Universidad-Cenfotec/Sumobot/códigos_de_ejemplo/Libreria HCSR04/8.x (DEPRECADO)/README.md

> ⚠️ **AVISO IMPORTANTE – VERSIÓN DEPRECADA** ⚠️  
> **Sumobot – Universidad CENFOTEC**

Las **primeras versiones del Sumobot de la Universidad CENFOTEC** utilizaban **IdeaBoards de CRCibernética** con firmware **CircuitPython 8.2.0**.

Actualmente, **esta versión y toda la rama 8.x de CircuitPython se encuentran deprecadas**, por lo que:
- ❌ No reciben soporte oficial
- ❌ No se recomienda su uso en nuevos desarrollos

Asimismo, **CRCibernética ya distribuye las placas IdeaBoard con versiones de firmware actuales**, alineadas con CircuitPython 9.x y superiores.

### Estado de esta librería
La librería correspondiente a **CircuitPython 8.x** se considera **obsoleta**, **Archivada** y es conservada únicamente con fines de **documentación histórica** y **compatibilidad retroactiva**

No se realizarán mejoras ni correcciones sobre esta versión.

### ✅ Recomendación
Se recomienda **actualizar el firmware de la IdeaBoard** a una versión moderna de CircuitPython para:
- Mantener compatibilidad con el desarrollo actual del Sumobot  
- Acceder a mejoras de rendimiento y estabilidad  
- Asegurar soporte futuro

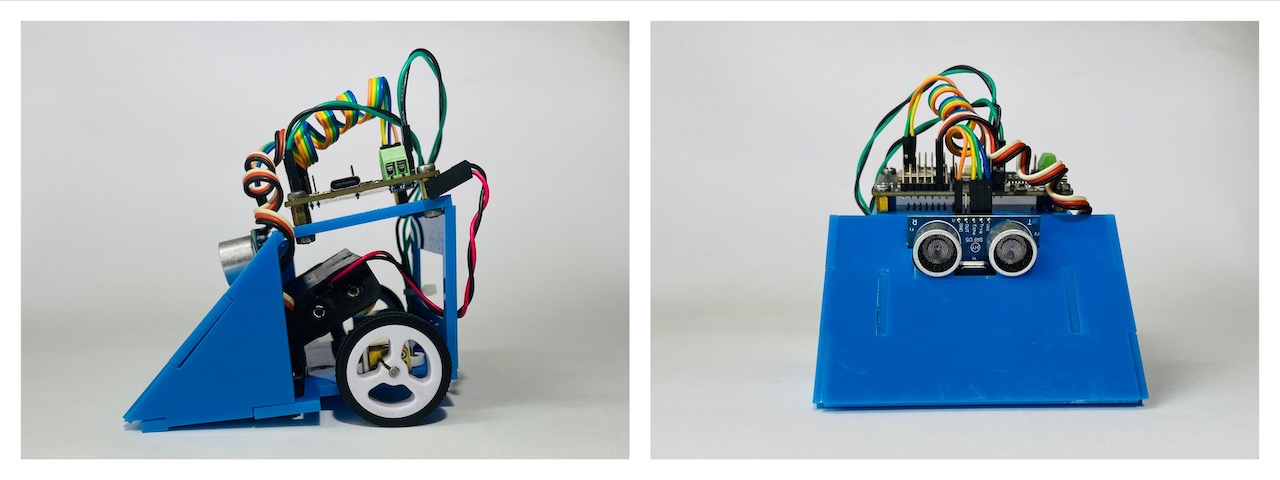
[picture p18: imagenes/SumoBot_1.JPG]
Sumobot Legacy
