Universidad-Cenfotec/Sumobot/espiritu_sumobot.md

# El espíritu del Torneo Sumobot 

## Sobre el Sumobot

**Un espacio para aprender y disfrutar**

El Sumobot no es solo una competencia.
Es un espacio donde venimos a aprender, probar ideas y pasarla bien.

Aquí construir es importante.
Pensar es importante.
Pero también lo es jugar.

En el Sumobot somos:

* Personas que construyen (**homo faber**)
* Personas que piensan (**homo sapiens**)
* Personas que disfrutan el juego (**homo ludens**)
* Personas que crean con tecnología (**homo ciberneticus**)

### ¿Qué significa competir aquí?

Aunque nuestros robots “luchan”, esto no es violencia.
Es una forma de poner a prueba ideas.

Cada combate es una oportunidad para aprender algo nuevo:
qué funciona, qué no, y qué podemos mejorar.

Aquí no se trata solo de ganar,
se trata de **entender lo que hacemos**.

### ¿Y si hay problemas?

En el Sumobot, los problemas se resuelven **hablando**.

* Las reglas no son solo para obedecerlas, son para entenderlas
* Si algo no es justo, se puede conversar
* Escuchar a los demás es parte del juego
* Resolver conflictos también es aprender

No estamos aquí para pelear entre nosotros,
estamos aquí para aprender juntos.

### Lo importante

* Disfrutar lo que hacemos
* Aprender de los errores
* Respetar a los demás
* Intentar cosas nuevas

Al final, lo más valioso no es el resultado,
es lo que aprendimos en el camino.
