Universidad-Cenfotec/Sumobot/instala_thonny.md

# **Cómo instalar Thonny y preparar el Sumobot para programarlo**

1. **Descargar Thonny**

   * Abre tu navegador y busca **“Thonny Python”**.
   * Ingresa al sitio oficial y descarga la versión correspondiente a tu sistema operativo (Windows, Mac o Linux).

2. **Instalar Thonny**

   * Ejecuta el instalador descargado.
   * En el asistente de instalación, presiona **Next** y acepta los términos.
   * Mantén las configuraciones por defecto (no es necesario cambiar nada).
   * Activa la opción para crear un acceso directo en el escritorio y haz clic en **Install**.
   * Al finalizar, presiona **Finish**.

3. **Abrir Thonny**

   * Busca **Thonny** en el menú de inicio y ábrelo.
   * La primera vez, selecciona el idioma (inglés o español según tu preferencia).

4. **Configurar el intérprete**

   * En el menú superior selecciona: **Tools → Options → Interpreter**.
   * Cambia el intérprete a **“CircuitPython (generic)”**.

5. **Conectar el Sumobot**

   * Conecta el cable **USB-C** al puerto del Sumobot.
   * Conecta el otro extremo **USB** a tu computadora.
   * Verifica que el dispositivo aparezca en el listado de puertos dentro de Thonny.

6. **Explorar los archivos del Sumobot**

   * En el panel de archivos de Thonny verás dos ubicaciones: tu computadora y el dispositivo **CircuitPython**.
   * Haz doble clic en el archivo **`code.py`** para abrir el programa que controla el robot.

7. **Listo para programar**

   * A partir de este punto, podrás modificar el archivo `code.py` y cargar tus programas al Sumobot.

**Tip:** Trabaja únicamente sobre el archivo `code.py` para mantener el funcionamiento correcto del robot.
