Universidad-Cenfotec/Sumobot/uso_thonny.md

# **Cómo programar el Sumobot usando Thonny**

1. **Conectar el Sumobot a la computadora**

   * Usa el cable incluido con el Sumobot.
   * Conecta el extremo **USB-C** al puerto del Sumobot.
   * Conecta el otro extremo **USB** a tu computadora.
   * En algunas computadoras escucharás un sonido al reconocer el dispositivo.

2. **Abrir Thonny**

   * Ejecuta el programa **Thonny** (ícono con las letras *Th*).

3. **Configurar el intérprete**

   * En el menú superior selecciona: **Herramientas → Opciones**.
   * Ve a la pestaña **Intérprete**.
   * Selecciona el puerto donde está conectado el Sumobot (en Windows aparece como “COMx”, en Mac como un nombre diferente).
   * Presiona **OK**.

4. **Explorar el contenido del Sumobot**

   * A la izquierda abajo verás el panel de archivos: ahí aparece lo que está guardado dentro del Sumobot.
   * A la izquierda arriba, Thonny muestra los archivos de tu computadora.

5. **Abrir el programa principal**

   * Haz doble clic en el archivo **`code.py`** (o **`code.p`**, según la versión) que aparece en el Sumobot.
   * Este archivo contiene el programa actual que controla el robot.

6. **Modificar el código**

   * Edita el contenido de `code.py` según el comportamiento que quieras programar (por ejemplo, cómo reaccionar ante los sensores o cómo mover los motores).

7. **Ejecutar el programa**

   * Presiona el botón **Ejecutar (Run)** o la tecla **F5**.
   * Thonny guardará los cambios en el Sumobot y ejecutará el nuevo programa.

8. **Probar y ajustar**

   * Interactúa con el robot (por ejemplo, cubriendo los sensores infrarrojos) para verificar el comportamiento.
   * Haz los ajustes necesarios al código y vuelve a ejecutar.
