Universidad-Cenfotec/Sumobot/códigos_de_ejemplo/control_fuzzy.md

### ¿Qué es un sistema de control difuso?

Tomás de Camino Beck, Ph.D.  
Universidad CENFOTEC

En muchas situaciones del mundo real, las decisiones no son simplemente **sí o no**, o **blanco o negro**. Por ejemplo, si vas caminando y alguien te pregunta si tienes calor, podrías decir: “**un poco**”, “**bastante**” o “**demasiado**”. Estas respuestas no son exactas, pero son útiles. En ingeniería y robótica, la **lógica difusa** nos permite trabajar con este tipo de información “borrosa” para tomar decisiones más humanas y suaves.

Un **sistema de control difuso** es una manera de hacer que un robot tome decisiones basadas en grados de verdad. En lugar de decir “el robot está exactamente desviado”, podemos decir “el robot está **ligeramente desviado**” o “**muy desviado**”. Y con eso, el robot puede corregir su movimiento poco o mucho, según lo que necesite.

---

### ¿Para qué sirve en un robot como el Sumobot?

En el caso de un robot como el **Sumobot**, que debe moverse en línea recta, es común que se desvíe un poco hacia un lado, por ejemplo si un motor gira más rápido que el otro. Usando un **giroscopio**, el robot puede medir ese desvío, es decir, cuánto está girando sin querer.

Un sistema de control difuso puede ayudar a corregir ese giro. ¿Cómo? Vamos a verlo con un ejemplo.

---

### Ejemplo simple: Corregir el movimiento recto usando el giroscopio

Imaginemos que el giroscopio le dice al robot cuánto se está girando: si el valor es cero, va perfectamente recto. Si es negativo, se está desviando a la izquierda. Si es positivo, a la derecha.

Podemos clasificar esos giros en grupos:

* **Negativo grande** → se está desviando mucho a la izquierda
* **Negativo pequeño** → se está desviando un poco a la izquierda
* **Cero** → va recto
* **Positivo pequeño** → se está desviando un poco a la derecha
* **Positivo grande** → se está desviando mucho a la derecha

A cada uno de esos grupos le asignamos un nombre difuso como “**muy izquierda**”, “**poco izquierda**”, “**centro**”, “**poco derecha**” y “**muy derecha**”.

Luego, le decimos al robot qué hacer para cada caso. Por ejemplo:

* Si se está desviando **mucho a la izquierda**, entonces hay que aumentar mucho la velocidad del motor izquierdo y disminuir la del derecho.
* Si se está desviando **poco a la derecha**, entonces basta con un pequeño ajuste.
* Si va **recto**, entonces ambos motores siguen igual.

Este tipo de decisiones se calculan con fórmulas que combinan los valores de desvío con cuánto pertenece ese valor a cada grupo difuso. El resultado final es un número que indica **cuánto debe corregir** el robot su movimiento. Esto se llama **desfusificación**, y permite transformar las reglas difusas en una acción concreta: por ejemplo, cuánto cambiar la velocidad de los motores.

---

### ¿Por qué es útil?

A diferencia de los sistemas que usan solo “si está mal, corrige todo”, el sistema difuso es más **suave**, más **inteligente** y permite que el robot se mueva de forma **más natural y precisa**. Se parece más a cómo corregimos nosotros mismos cuando caminamos o andamos en bicicleta: no damos giros bruscos si solo nos desviamos un poco.
