Universidad-Cenfotec/Sumobot/códigos_de_ejemplo/programación_física/Cuadrícula.jpeg

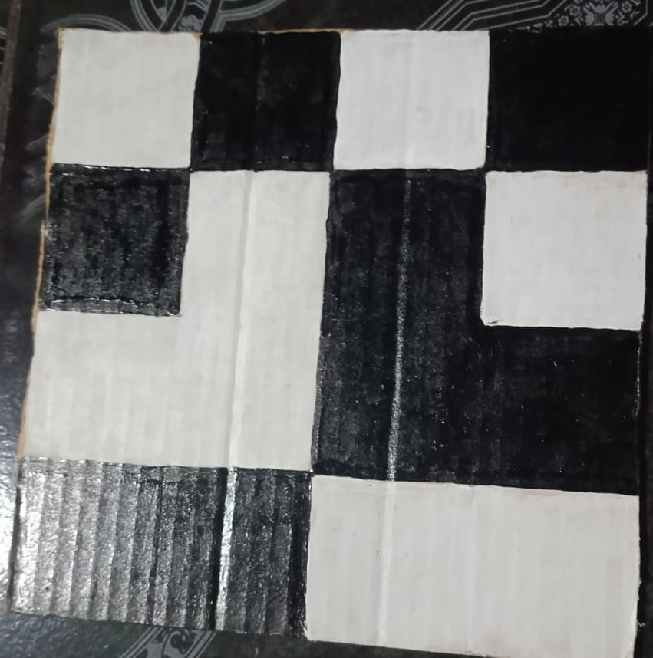
códigos_de_ejemplo/programación_física/Cuadrícula.jpeg
