Universidad-Cenfotec/Sumobot/imagenes/chasis2025.JPG

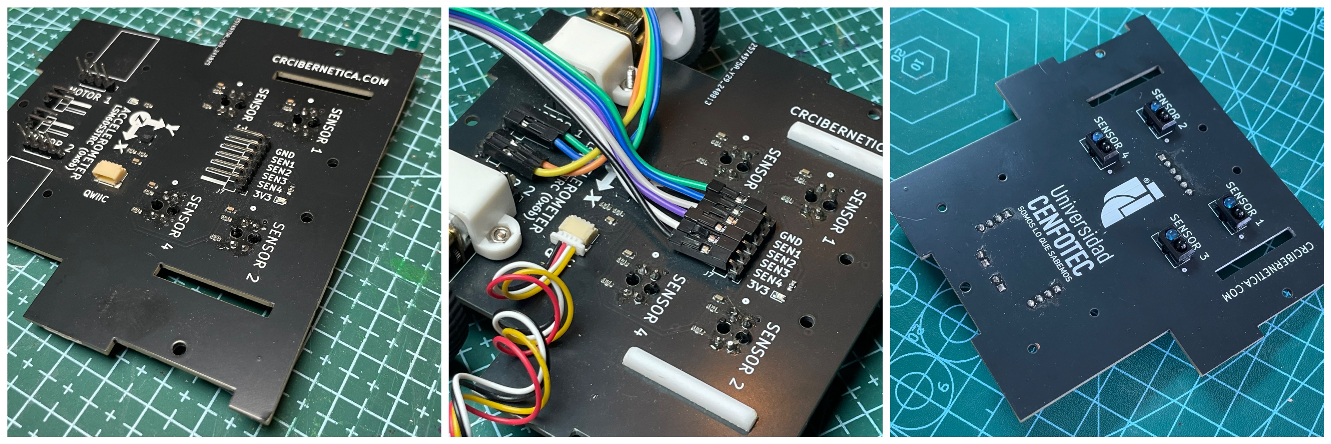
imagenes/chasis2025.JPG
