Universidad-Cenfotec/Sumobot/imagenes/motores_soldar.jpeg

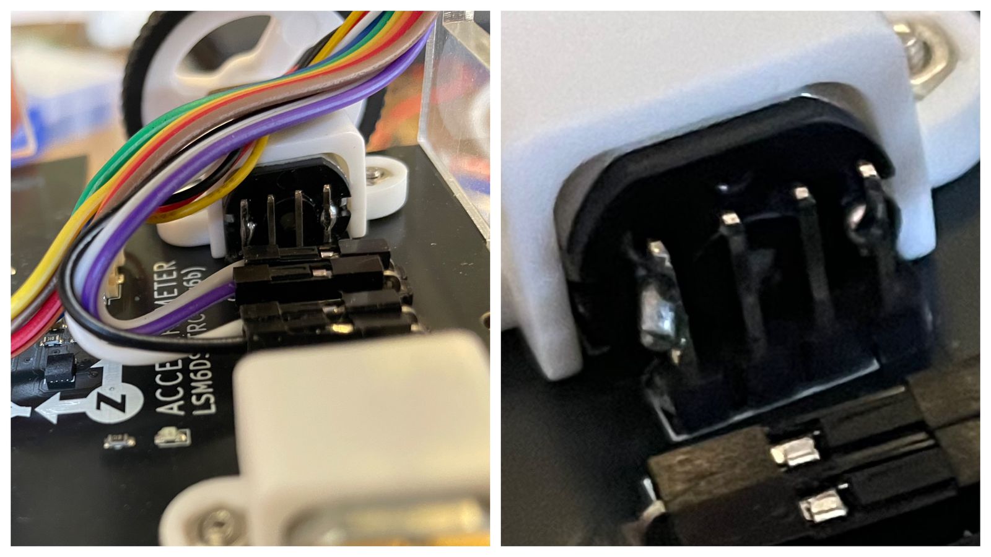
imagenes/motores_soldar.jpeg
