Universidad-Cenfotec/Sumobot/imagenes/SumoBot_Dojo.JPG

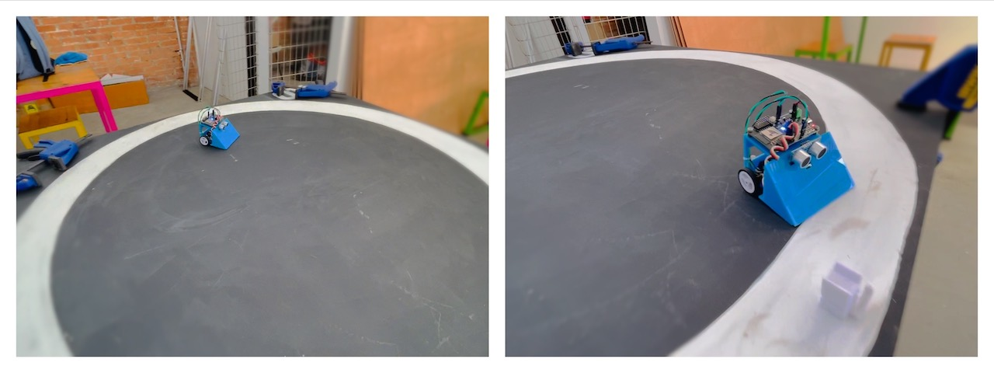
imagenes/SumoBot_Dojo.JPG
