Universidad-Cenfotec/Sumobot/archivos_de_fabricacion/Old/README.md

> **Nota:** Estos archivos fueron creados antes del rediseño de 2025 y se mantienen como documentación archivada sobre la creación del SumoBot de la Universidad CENFOTEC.

# Archivos de fabricación del Chasis
1. **chasis_sumobot.dxf**: Este archivo está en formato DXF (Drawing Exchange Format), que es utilizado comúnmente para intercambiar datos de dibujos entre diferentes programas de diseño asistido por computadora (CAD). Se utiliza frecuentemente para precisar las dimensiones y el diseño del chasis del robot, incluyendo cortes y perforaciones.

2. **chasis_sumobot.rld**: Este archivo es un archivo de corte láser, típicamente usado en máquinas de corte láser para interpretar el diseño y realizar cortes precisos en materiales como metal o plástico. El formato RLD es específico para ciertos tipos de software o controladores de máquinas de corte.

3. **chasis_sumobot.svg**: Un archivo SVG (Scalable Vector Graphics) es un formato de gráficos vectoriales que puede ser usado para diseño web y también en impresión y cortes de precisión. En el contexto de la fabricación de un chasis de sumobot, este archivo podría utilizarse para proporcionar una visualización detallada de componentes individuales o del diseño decorativo del chasis.

4. **chasis_sumobot2024_3D.stl**: Este archivo en formato STL (STereoLithography) es ampliamente usado en impresión 3D. Contiene la información geométrica de un modelo 3D del chasis del sumobot. Es esencial para la creación de prototipos y la producción final de partes del robot mediante impresión 3D.

Imagen Corte

## Modificación del Chasis

También puede utilizar [este archivo](https://www.tinkercad.com/things/2SyTLlaZ3rV-sumobot6?sharecode=ivtFQecJ67wsbuyDAFKAAIibqH1ZuByYk1oDVZOuIXM) en Tinkercad para hacer modificaciones del diseño, o separar partes
