Universidad-Cenfotec/Sumobot/códigos_de_ejemplo/codigo inicio/code.py

# Tomás de Camino Beck
# Escuela de Sistemas Inteligentes
# Universidad Cenfotec

import board  # Librerías para accesar a I/O de la placa
import keypad  # Para leer el botón BOOT
from ideaboard import IdeaBoard  # Librería de funciones varias del ideaboard
from time import sleep  # Para utilizar función que detiene el código
from hcsr04 import HCSR04  # Librerías para el sensor de Ultrasonido
import random  # Librerías de números aleatorios

sonar = HCSR04(board.IO25, board.IO26)  # Crea una instanciación del sensor ultrasonido

ib = IdeaBoard()  # Instanciación I/O y funciones del Ideaboard

# Configura botón BOOT en IO0
keys = keypad.Keys((board.IO0,), value_when_pressed=False, pull=True)

# Configura los pines analógicos donde están conectados los sensores infrarrojos
sen1 = ib.AnalogIn(board.IO36)  # SENSOR 1 (adelante izquierdo) pin IO36
sen2 = ib.AnalogIn(board.IO39)  # SENSOR 2 (adelante derecho) pin IO39
sen3 = ib.AnalogIn(board.IO34)  # SENSOR 3 (atrás izquierdo) pin IO34
sen4 = ib.AnalogIn(board.IO35)  # SENSOR 4 (atrás derecho) pin IO35

# Crea una lista con los sensores infrarrojos para poder recorrerlos fácilmente
infrarrojos = [sen1, sen2, sen3, sen4]


# Función que convierte a entero base 10
# Utiliza desplazamiento de bits
def arreglo_a_entero(bits):
    valor = 0
    for bit in bits:
        valor = (valor << 1) | bit
    return valor


# Arreglo de 0 y 1s (0-blanco, 1-negro)
def leer_sensores(infrarrojos, valor_critico=10000):
    return [int(sen.value < valor_critico) for sen in infrarrojos]


def on_white(infrarrojos, valor_critico=10000):
    sensores = leer_sensores(infrarrojos, valor_critico)
    return arreglo_a_entero(sensores) > 0


def line_status(infrarrojos, valor_critico=10000):
    sensores = leer_sensores(infrarrojos, valor_critico)
    return arreglo_a_entero(sensores)


def wiggle(t, n, speed):
    # Hace que el robot se mueva izquierda y derecha
    # por tiempo t, a velocidad speed = [0,1]
    # lo hace n veces
    for i in range(n):
        ib.pixel = (0, 0, 255)
        ib.motor_1.throttle = -speed
        ib.motor_2.throttle = speed
        sleep(t)
        ib.motor_1.throttle = speed
        ib.motor_2.throttle = -speed
        sleep(t)
        stop()
        sleep(t)
        ib.pixel = (0, 0, 255)
        ib.motor_1.throttle = speed
        ib.motor_2.throttle = -speed
        sleep(t)
        ib.motor_1.throttle = -speed
        ib.motor_2.throttle = speed
        sleep(t)


def wiggle_forward(t, n, speed):
    # Hace que el robot se mueva izquierda y derecha
    # por tiempo t, a velocidad speed = [0,1]
    # lo hace n veces
    for i in range(n):
        ib.pixel = (0, 0, 255)
        ib.motor_1.throttle = -speed
        ib.motor_2.throttle = speed
        sleep(t)
        ib.motor_1.throttle = speed
        ib.motor_2.throttle = -speed
        sleep(t)
        stop()
        sleep(t)
        stop()
        forward(0.3, 1)
        sleep(t)
        ib.pixel = (0, 0, 255)
        ib.motor_1.throttle = speed
        ib.motor_2.throttle = -speed
        sleep(t)
        ib.motor_1.throttle = -speed
        ib.motor_2.throttle = speed
        sleep(t)


def forward(t, speed):
    # Mueve el robot hacia adelante
    # por tiempo t, a velocidad speed = [0,1]
    ib.pixel = (0, 255, 0)
    ib.motor_1.throttle = speed
    ib.motor_2.throttle = speed
    sleep(t)


def backward(t, speed):
    # Mueve el robot hacia atrás
    # por tiempo t, a velocidad speed = [0,1]
    ib.pixel = (150, 255, 0)
    ib.motor_1.throttle = -speed
    ib.motor_2.throttle = -speed
    sleep(t)


def left(t, speed):
    # Mueve el robot hacia la izquierda
    # por tiempo t, a velocidad speed = [0,1]
    ib.pixel = (50, 55, 100)
    ib.motor_1.throttle = -speed
    ib.motor_2.throttle = speed
    sleep(t)


def right(t, speed):
    # Mueve el robot hacia la derecha
    # por tiempo t, a velocidad speed = [0,1]
    ib.pixel = (50, 55, 100)
    ib.motor_1.throttle = speed
    ib.motor_2.throttle = -speed
    sleep(t)


def stop():
    # Detiene los motores
    ib.pixel = (0, 0, 0)
    ib.motor_1.throttle = 0
    ib.motor_2.throttle = 0


def randomTurn(t, speed):
    # Escoge izq o der al azar y rota
    # por tiempo t, a velocidad speed = [0,1]
    dir = random.choice([-1, 1])
    ib.pixel = (255, 0, 0)
    ib.motor_1.throttle = dir * -speed
    ib.motor_2.throttle = dir * speed
    sleep(t)


def lookForward():
    # Con el sensor ultrasónico mide la distancia al objeto de enfrente
    # retorna la distancia en centímetros
    stop()
    dist = sonar.dist_cm()
    sleep(0.2)
    return dist


def scan():
    # Se mueve hacia un lado buscando objetos delante
    # Se detiene luego de un número fijo de rotaciones
    # o cuando encuentra un objeto a la distancia indicada
    stop()
    maxCount = 10
    count = 0
    dist = lookForward()
    while count < maxCount and (dist > 30 or dist == -1):
        left(0.2, 0.2)
        count += 1
        dist = lookForward()
    stop()
    if count == maxCount:
        return False
    else:
        return True


def forwardCheck(t, speed, th):
    # Mueve el robot hacia adelante
    # por tiempo t, a velocidad speed = [0,1]
    # pero revisando el sensor IR para evitar salir del Dojo
    d = int(t / 0.01)
    for i in range(d):
        status = line_status(infrarrojos, th)
        print(status)
        if status == 0:
            forward(0.1, speed)
        elif status >= 1 and status <= 3:
            # toca linea blanca atrás... Full speed adelante!!!
            wiggle_forward(0.1, 4, 1)
        else:
            stop()
            sleep(0.3)
            backward(1, 0.3)
            randomTurn(1, 0.3)


def esperar_boton():
    # Espera hasta que el botón BOOT sea soltado
    print("Esperando botón...")
    ib.pixel = (255, 100, 0)  # naranja = esperando inicio

    while True:
        event = keys.events.get()
        if event and event.released:
            print("Botón soltado. Iniciando...")
            ib.pixel = (0, 255, 0)
            sleep(0.2)
            ib.pixel = (0, 0, 0)
            return


###### CODIGO PRINCIPAL #######
th = 2950

# Espera una sola vez antes de arrancar
stop()
esperar_boton()

# Loop principal
while True:
    distancia = sonar.dist_cm()
    if distancia > -1 and distancia < 30:
        right(0.1, 0.2)
        forwardCheck(0.2, 1, th)
        stop()
        sleep(0.3)
    else:
        stop()
        sleep(0.3)
        right(0.1, 0.2)
    stop()
