Universidad-Cenfotec/Sumobot/códigos_de_ejemplo/code_storage.py

#Tomás de Camino Beck
#Universidad CENFOTEC

import storage
from ideaboard import IdeaBoard
import time
import board
from hcsr04 import HCSR04 #

sonar =  HCSR04(board.IO26,board.IO25)



# Función para guardar datos
def guardar_datos(archivo: str, datos):
    """
    Guarda una lista de datos en un archivo CSV, añadiendo cada nueva entrada en una nueva línea.

    Args:
    archivo (str): El nombre del archivo donde se guardarán los datos.
    datos (list): Lista de datos (cualquier tipo que pueda ser convertido a string) para ser escritos en el archivo.

    Returns:
    None
    """   
    with open(archivo, "a") as f:
        f.write(",".join(str(d) for d in datos) + "\n")

# Loop principal
while True:
    try:
        distancia = sonar.dist_cm()
        print("Distancia:", distancia, "cm")
        guardar_datos("datos.csv",[distancia,distancia])
    except RuntimeError as e:
        print("Error al leer el sensor:", e)
    time.sleep(0.2)  # Esperar un segundo antes de la próxima medición
